albogdano/compaqt-portable-sffpc/3MF Files/1515_nuts.3mf

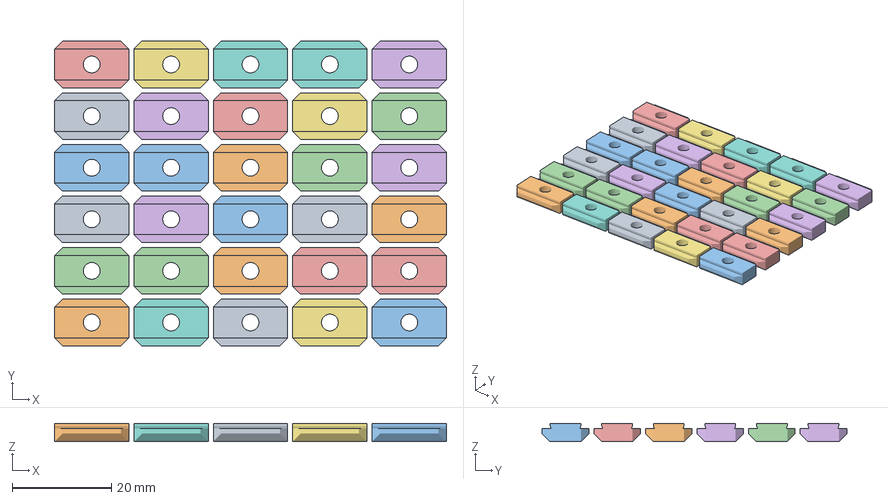
[picture p26: CAD file, 2025-07-14]
3MF Files/1515_nuts.3mf
79.0 x 61.4 x 3.69 mm
1515【螺帽组合滑块】.stl x 30
