albogdano/compaqt-portable-sffpc/3MF Files/ring_spacers.3mf

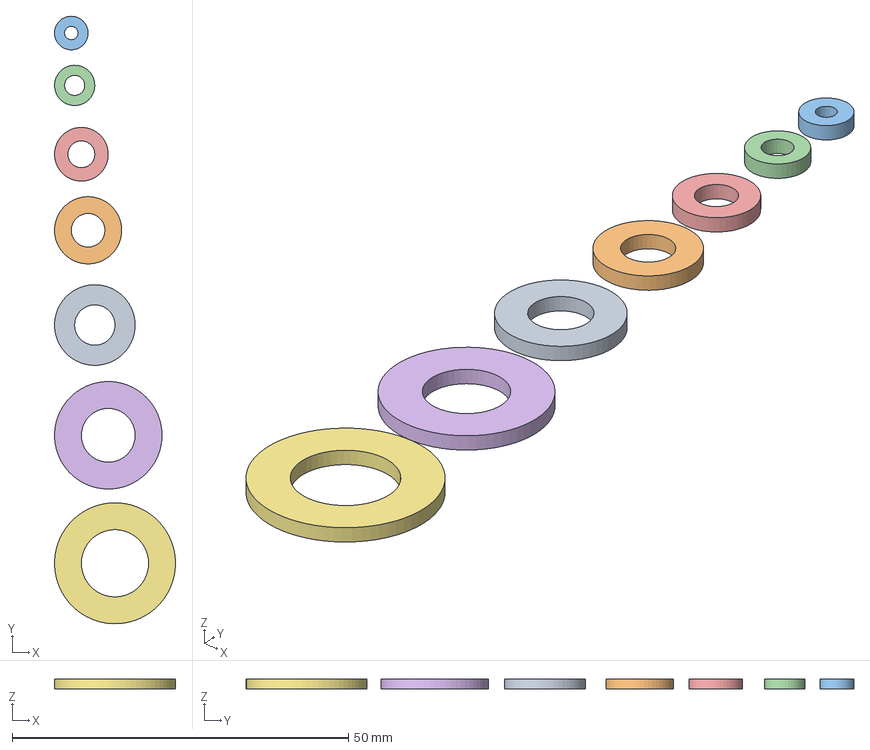
[picture p27: CAD file, 2025-07-14]
3MF Files/ring_spacers.3mf
18.0 x 90.4 x 1.50 mm
M2 10螺丝垫片.stl_2
M2 10螺丝垫片.stl_4
M2 10螺丝垫片.stl_5
M2 10螺丝垫片.stl_7
M2 10螺丝垫片.stl_9
M2 10螺丝垫片.stl_11
M2 10螺丝垫片.stl_13
