albogdano/compaqt-portable-sffpc/FreeCAD files/back_panel.FCStd

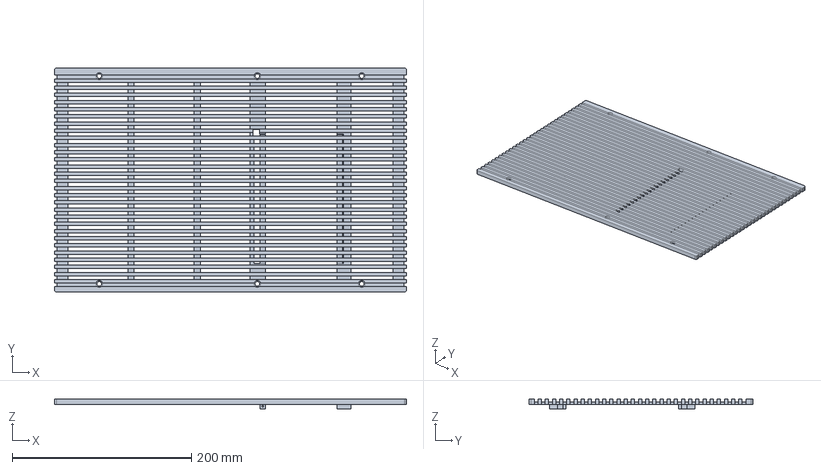
[picture p28: CAD file, 2025-07-14]
FreeCAD files/back_panel.FCStd
393.0 x 250.0 x 11.0 mm
