albogdano/compaqt-portable-sffpc/FreeCAD files/top_handle.FCStd

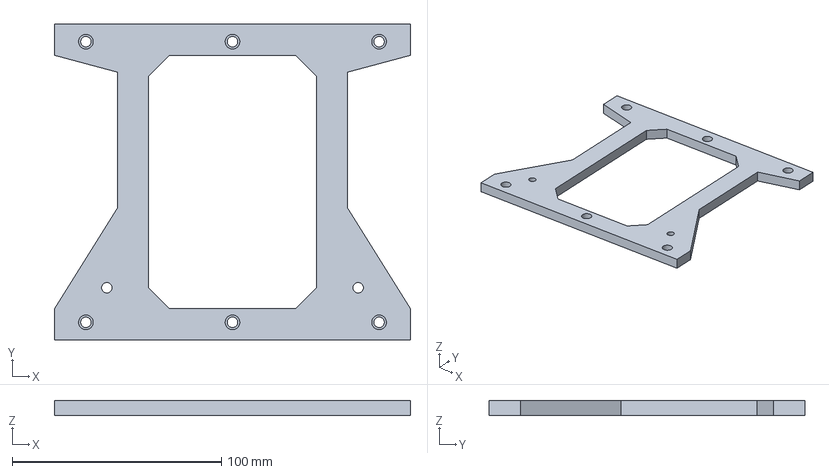
[picture p29: CAD file, 2025-07-14]
FreeCAD files/top_handle.FCStd
170.0 x 151.0 x 7.00 mm
