albogdano/compaqt-portable-sffpc/FreeCAD files/kb_bracket.FCStd

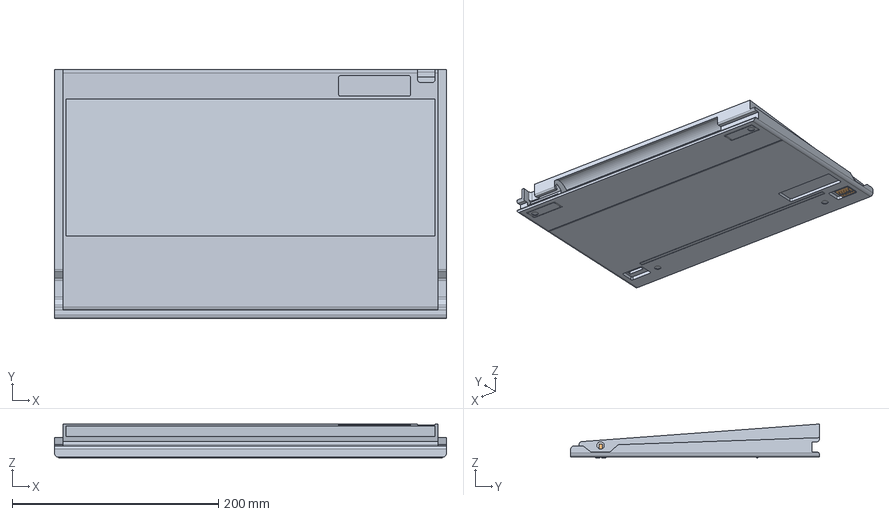
[picture p30: CAD file, 2025-07-14]
FreeCAD files/kb_bracket.FCStd
380.0 x 241.0 x 32.5 mm
Latch
