albogdano/compaqt-portable-sffpc/FreeCAD files/bottom_panel.FCStd

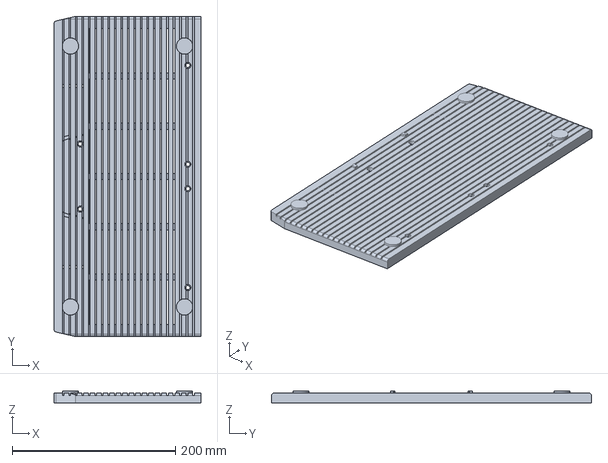
[picture p31: CAD file, 2025-07-14]
FreeCAD files/bottom_panel.FCStd
180.0 x 392.5 x 15.0 mm
