albogdano/compaqt-portable-sffpc/FreeCAD files/right_panel.FCStd

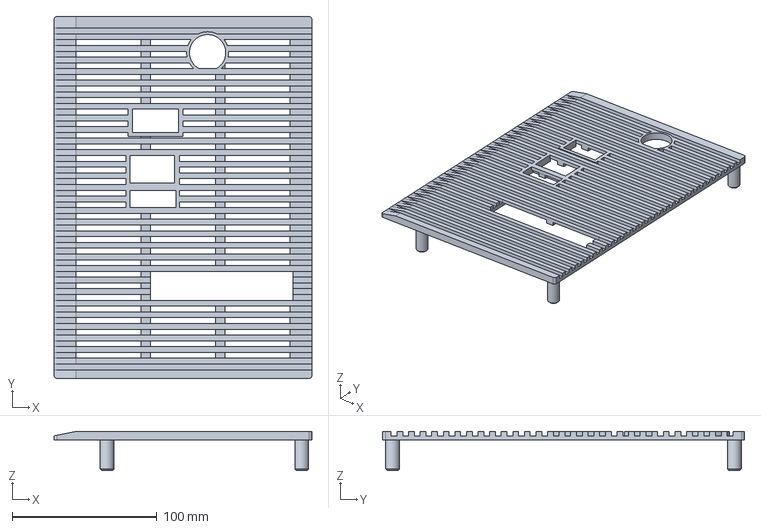
[picture p32: CAD file, 2025-07-14]
FreeCAD files/right_panel.FCStd
178.0 x 250.0 x 27.0 mm
